arielcruzf/Wireless-Welding-Pedal/HARDWARE/1NO-M16-switch-scheme.webp

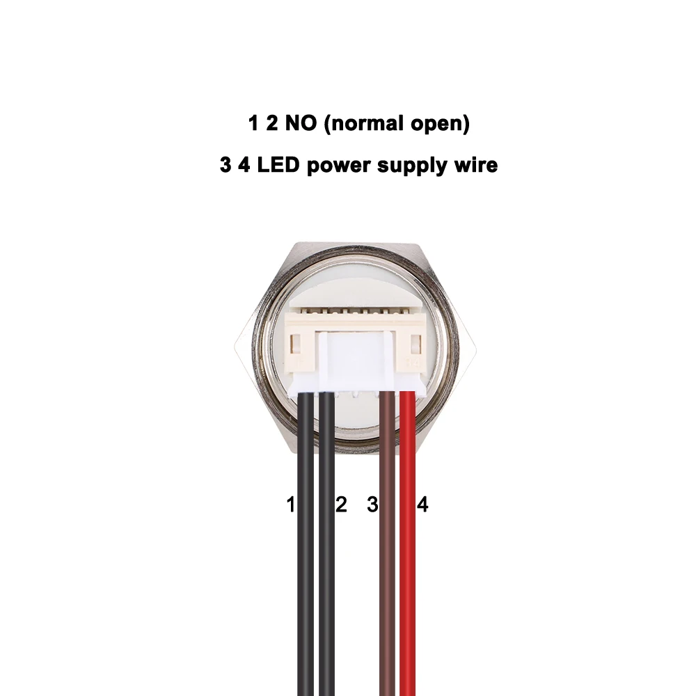
HARDWARE/1NO-M16-switch-scheme.webp
