arielcruzf/Wireless-Welding-Pedal/HARDWARE/BATTERY 103048 3.7V 1500mAh - 2.png

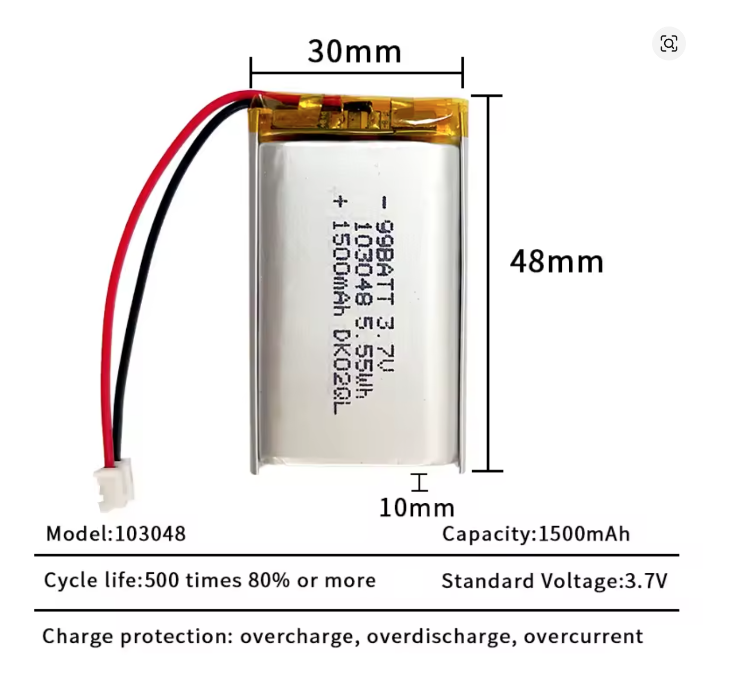
HARDWARE/BATTERY 103048 3.7V 1500mAh - 2.png
