arielcruzf/Wireless-Welding-Pedal/HARDWARE/BATTERY LIST.webp

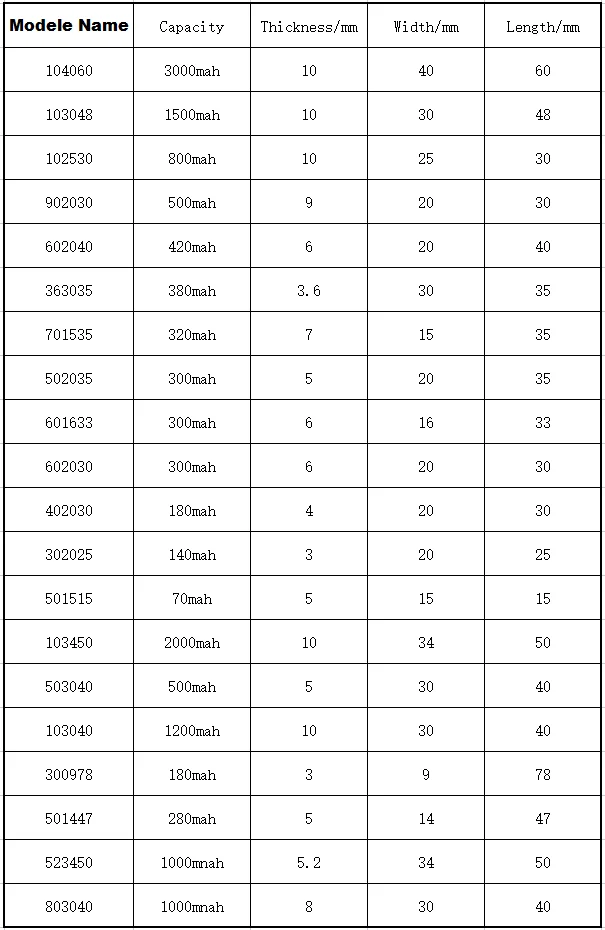
HARDWARE/BATTERY LIST.webp
