arielcruzf/Wireless-Welding-Pedal/HARDWARE/ESQUEMA.png

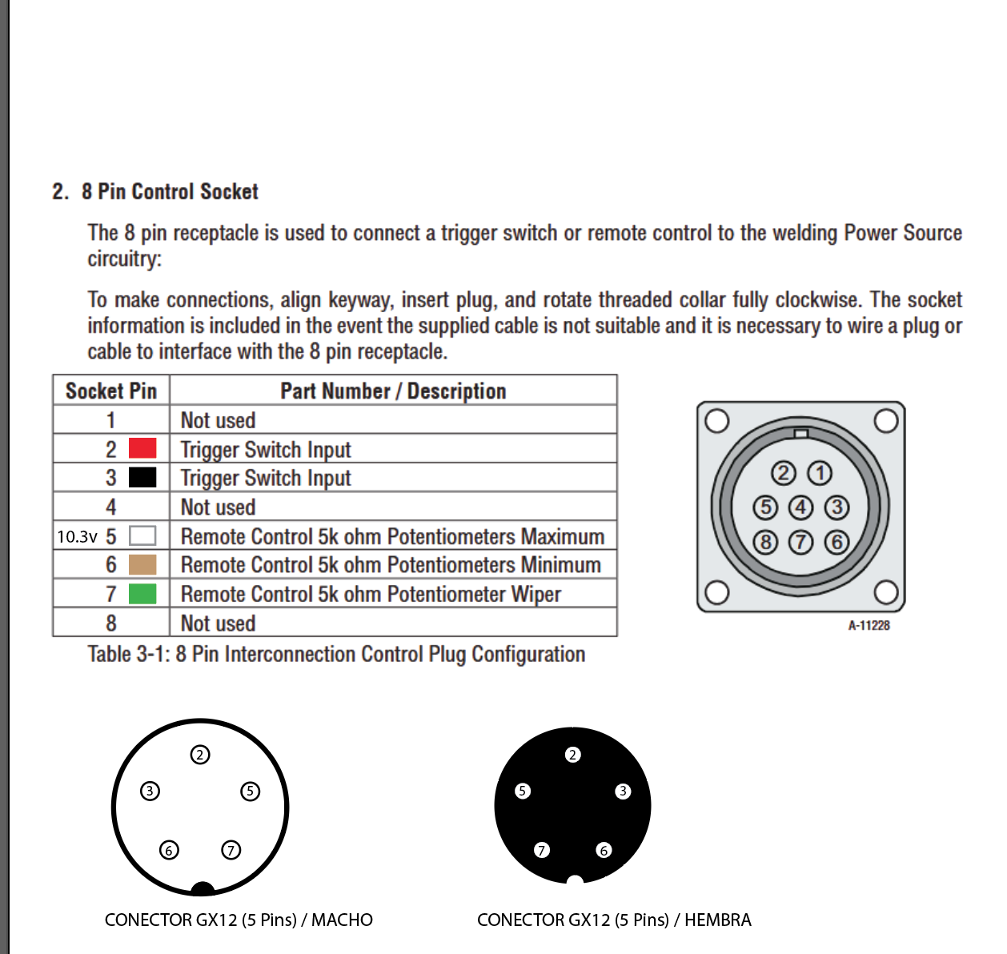
HARDWARE/ESQUEMA.png
