arielcruzf/Wireless-Welding-Pedal/HARDWARE/Flat 2D Vector Illustration - 1LiPo Battery 3.7V 1500mAh 103048.png

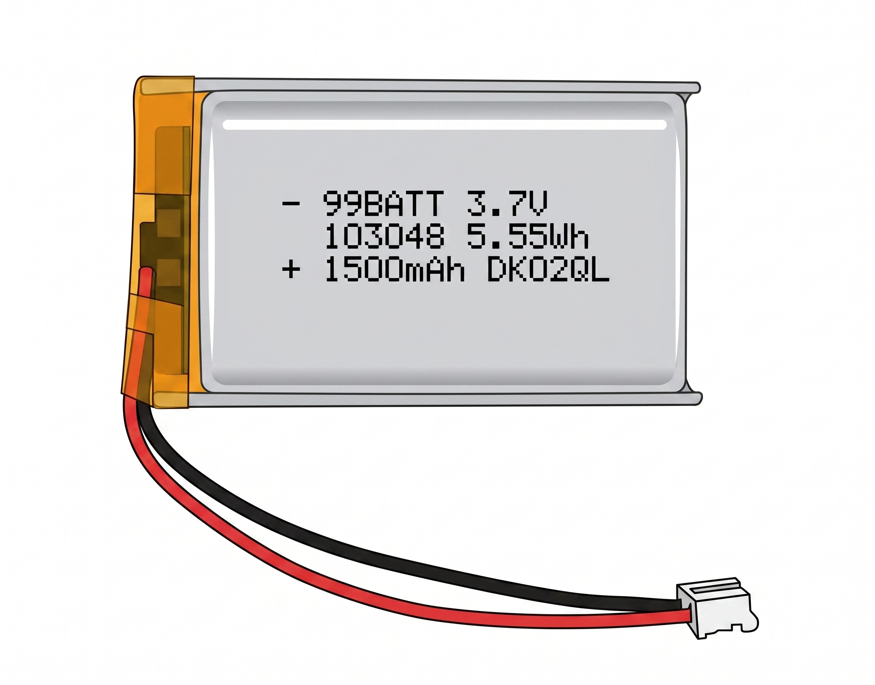
HARDWARE/Flat 2D Vector Illustration - 1LiPo Battery 3.7V 1500mAh 103048.png
