arielcruzf/Wireless-Welding-Pedal/HARDWARE/Flat 2D Vector Illustration - KW12 Limit Switch (16mm).png

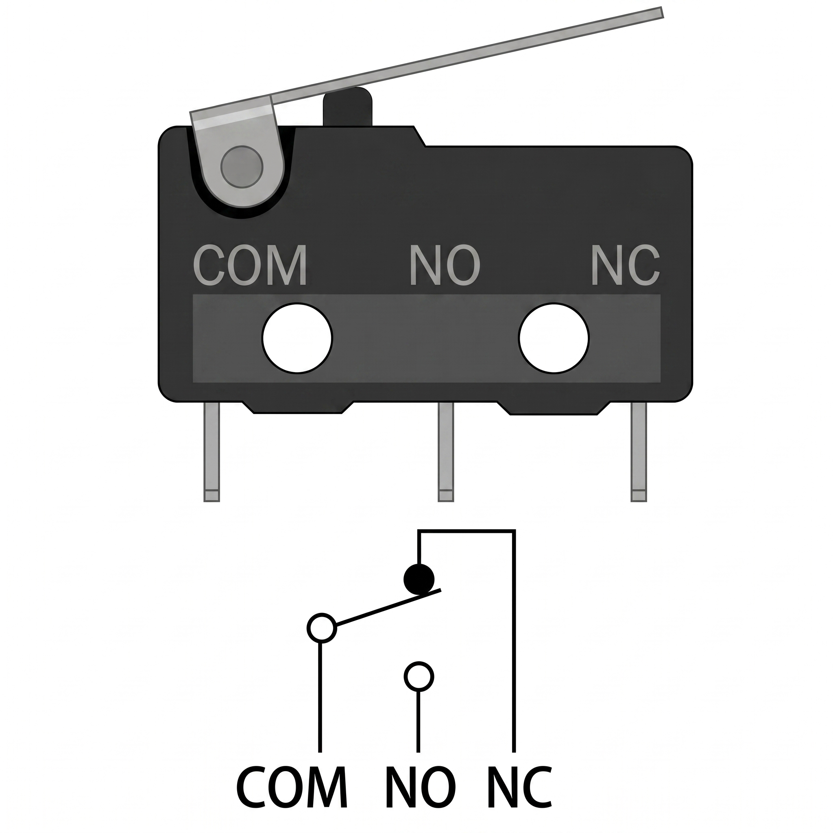
HARDWARE/Flat 2D Vector Illustration - KW12 Limit Switch (16mm).png
