arielcruzf/Wireless-Welding-Pedal/HARDWARE/Flat 2D Vector Illustration - LoRa32u4 RA-02 433MHz.png

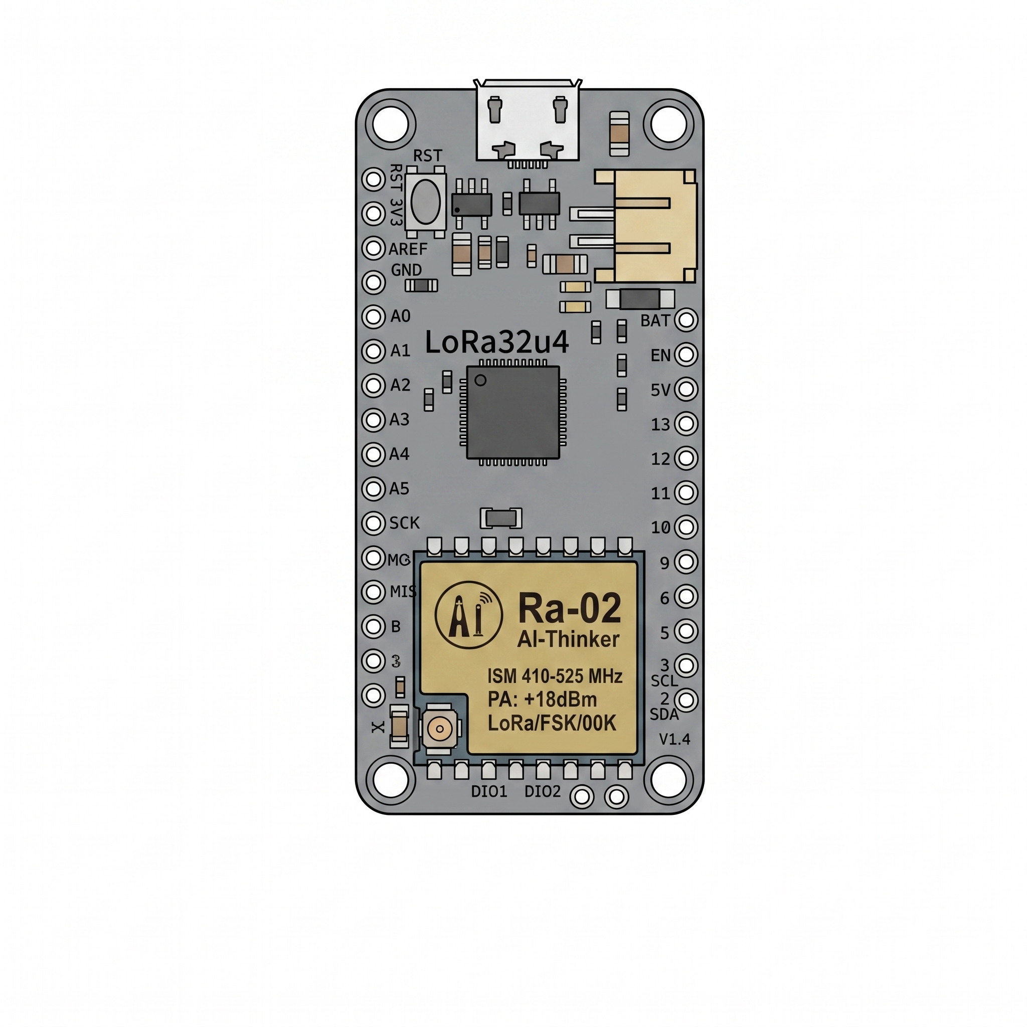
HARDWARE/Flat 2D Vector Illustration - LoRa32u4 RA-02 433MHz.png
