arielcruzf/Wireless-Welding-Pedal/HARDWARE/Flat 2D Vector Illustration - mosfet LR7843.png

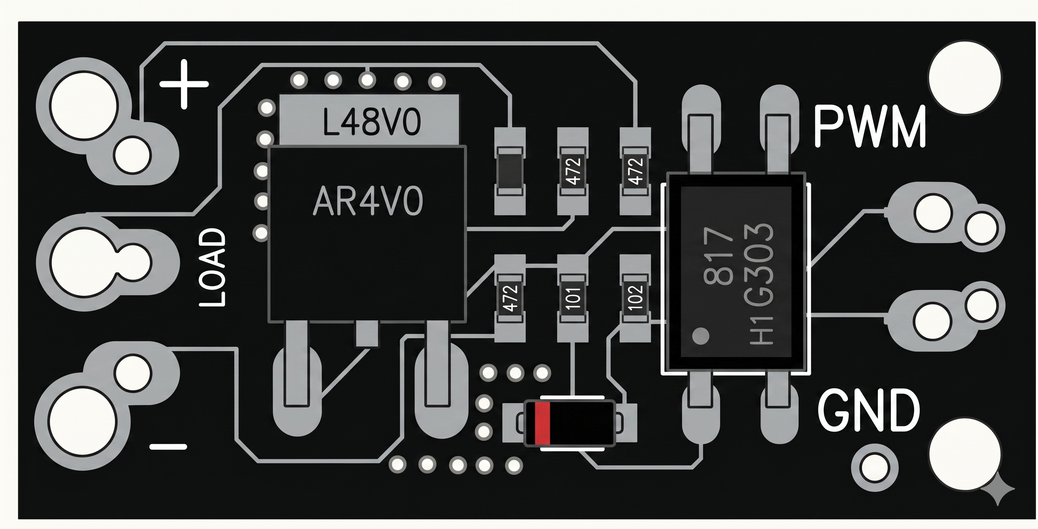
HARDWARE/Flat 2D Vector Illustration - mosfet LR7843.png
