arielcruzf/Wireless-Welding-Pedal/HARDWARE/Flat 2D Vector Illustration - OLED 128x32 SSD1306.png

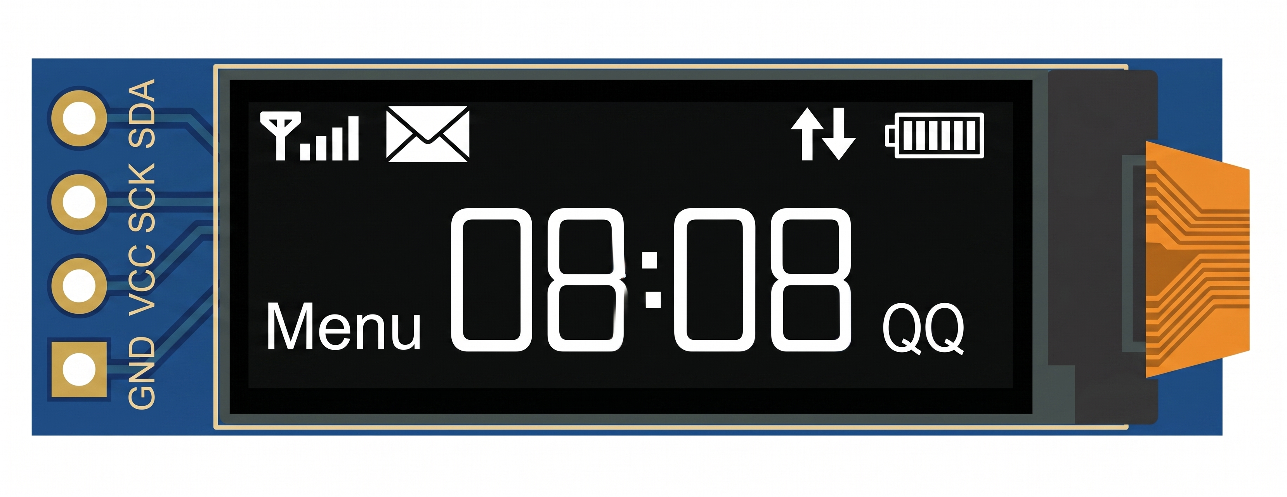
HARDWARE/Flat 2D Vector Illustration - OLED 128x32 SSD1306.png
