arielcruzf/Wireless-Welding-Pedal/HARDWARE/Flat 2D Vector Illustration - PWM-to-DAC Module (0-10V).png

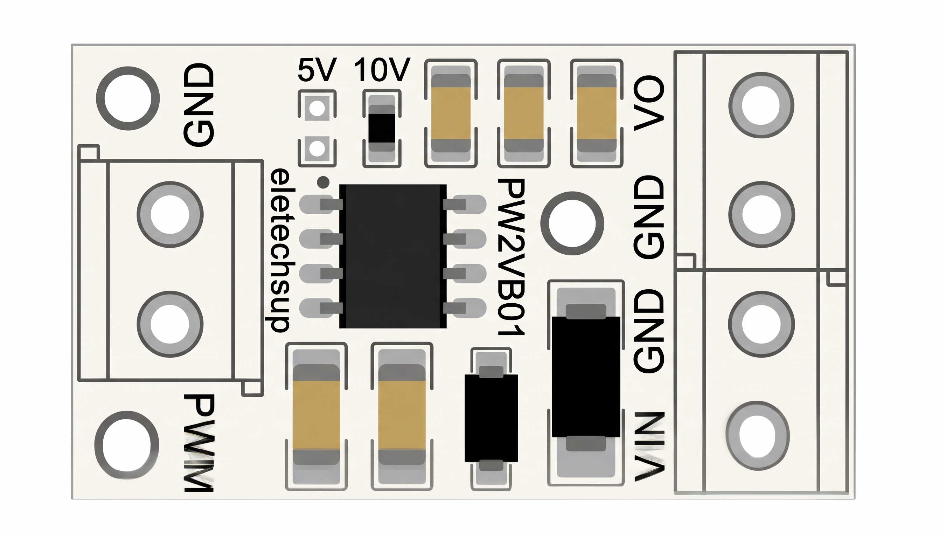
HARDWARE/Flat 2D Vector Illustration - PWM-to-DAC Module (0-10V).png
