arielcruzf/Wireless-Welding-Pedal/HARDWARE/Flat 2D Vector Illustration - VL53L4CD ToF Distance Sensor.png

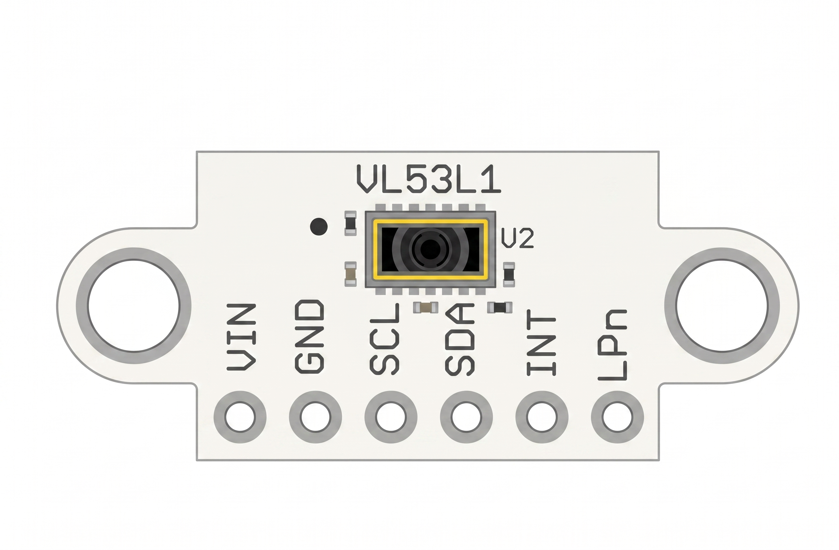
HARDWARE/Flat 2D Vector Illustration - VL53L4CD ToF Distance Sensor.png
