arielcruzf/Wireless-Welding-Pedal/HARDWARE/GX12-5PIN-M - 2.png

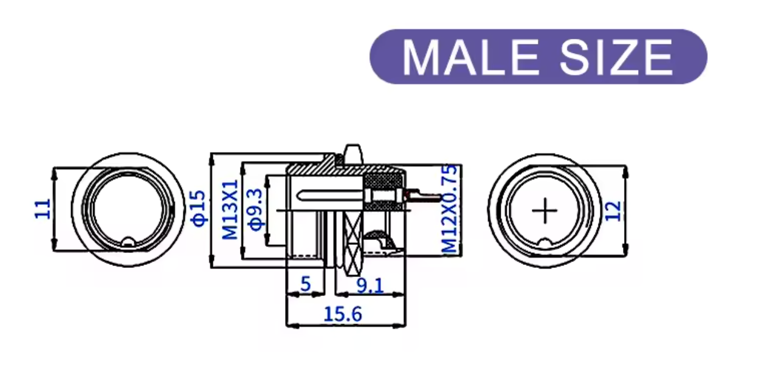
HARDWARE/GX12-5PIN-M - 2.png
