arielcruzf/Wireless-Welding-Pedal/HARDWARE/GX12-5PIN-M - 3.png

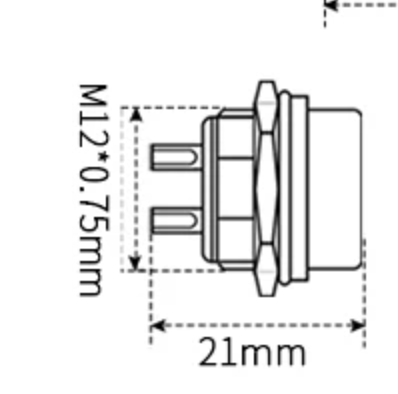
HARDWARE/GX12-5PIN-M - 3.png
