arielcruzf/Wireless-Welding-Pedal/HARDWARE/GX12-5PIN-M - 4.png

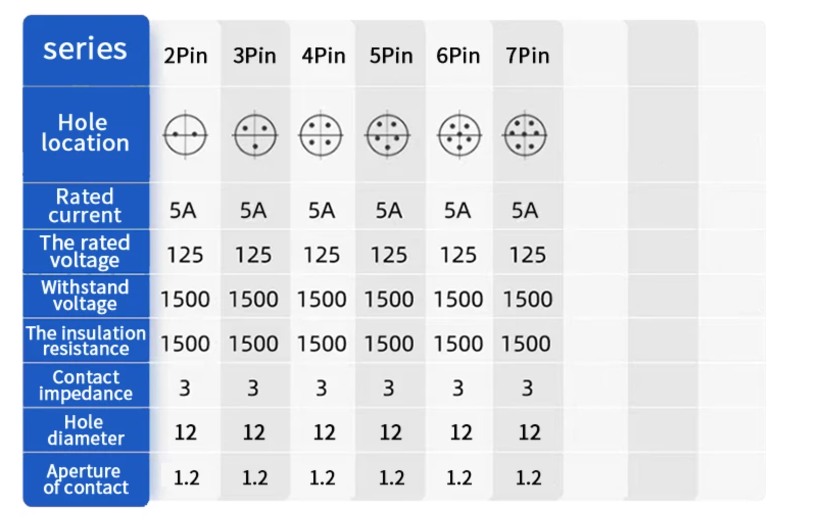
HARDWARE/GX12-5PIN-M - 4.png
