arielcruzf/Wireless-Welding-Pedal/HARDWARE/GX12-5PIN-M.png

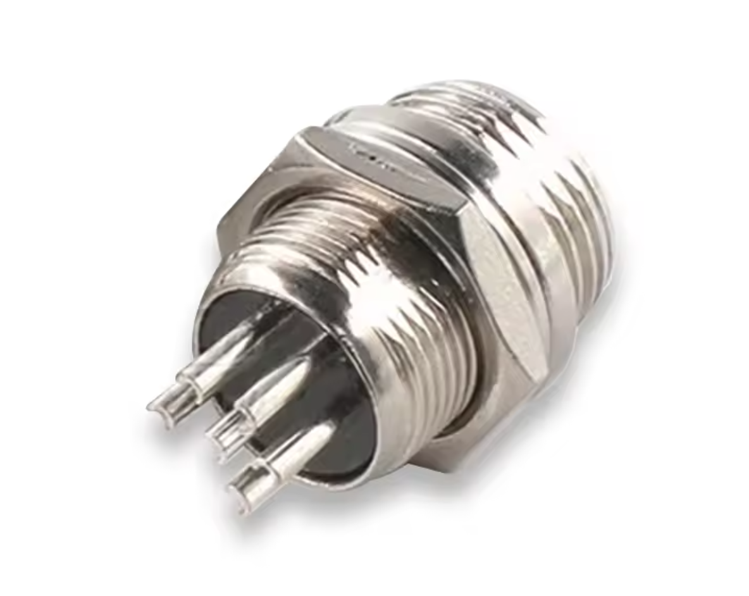
HARDWARE/GX12-5PIN-M.png
