arielcruzf/Wireless-Welding-Pedal/HARDWARE/LCD OLED 0.91 pulgadas 128x32 SSD1306 - 1.png

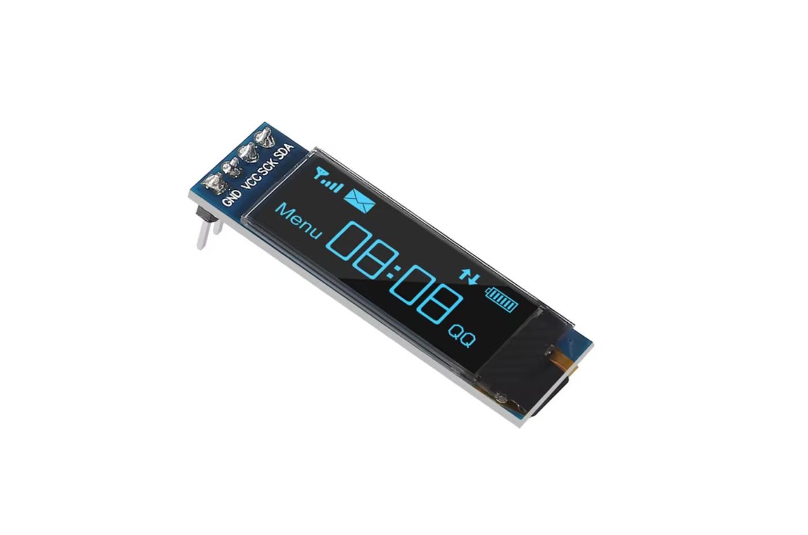
HARDWARE/LCD OLED 0.91 pulgadas 128x32 SSD1306 - 1.png
