arielcruzf/Wireless-Welding-Pedal/HARDWARE/LIMIT SWITCH - KW12  - 16mm.png

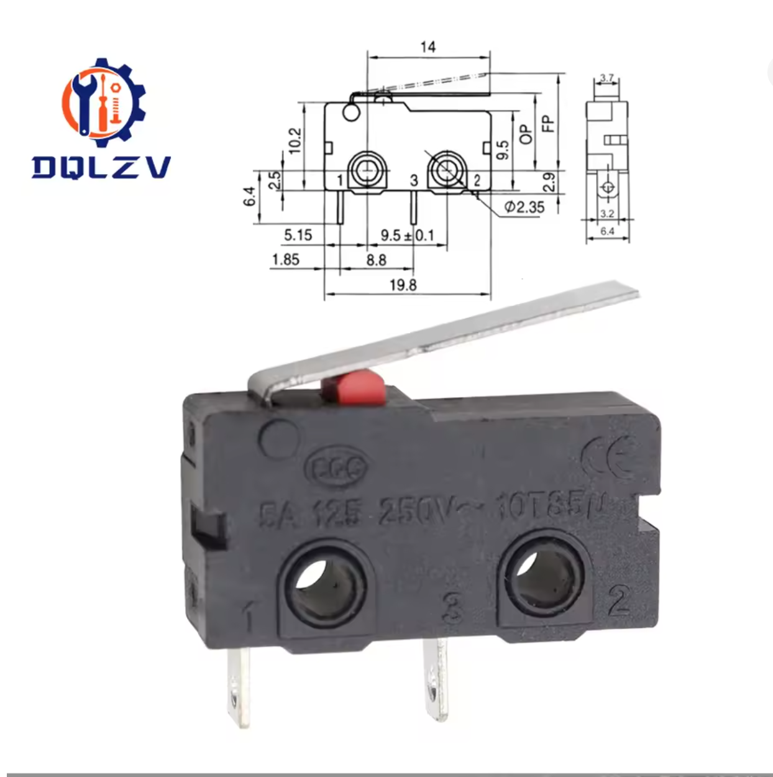
HARDWARE/LIMIT SWITCH - KW12 - 16mm.png
