arielcruzf/Wireless-Welding-Pedal/HARDWARE/LoRa32u4 RA-02 433MH - 1.webp

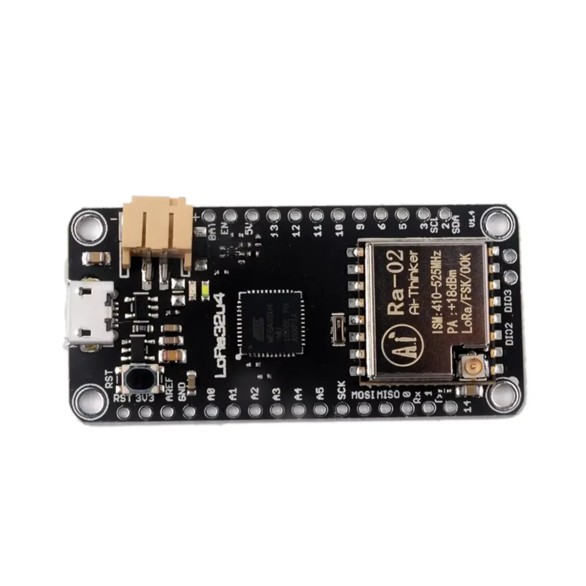
HARDWARE/LoRa32u4 RA-02 433MH - 1.webp
