arielcruzf/Wireless-Welding-Pedal/HARDWARE/LoRa32u4 RA-02 433MH.webp

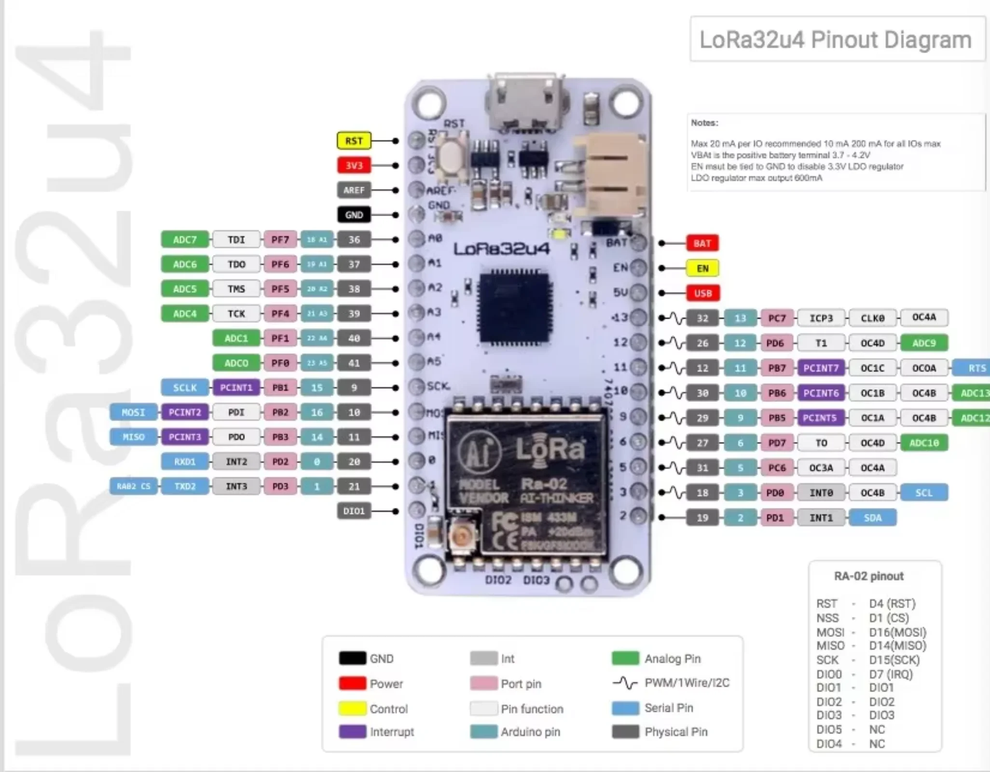
HARDWARE/LoRa32u4 RA-02 433MH.webp
