arielcruzf/Wireless-Welding-Pedal/HARDWARE/Lora32u4-scheme.jpg

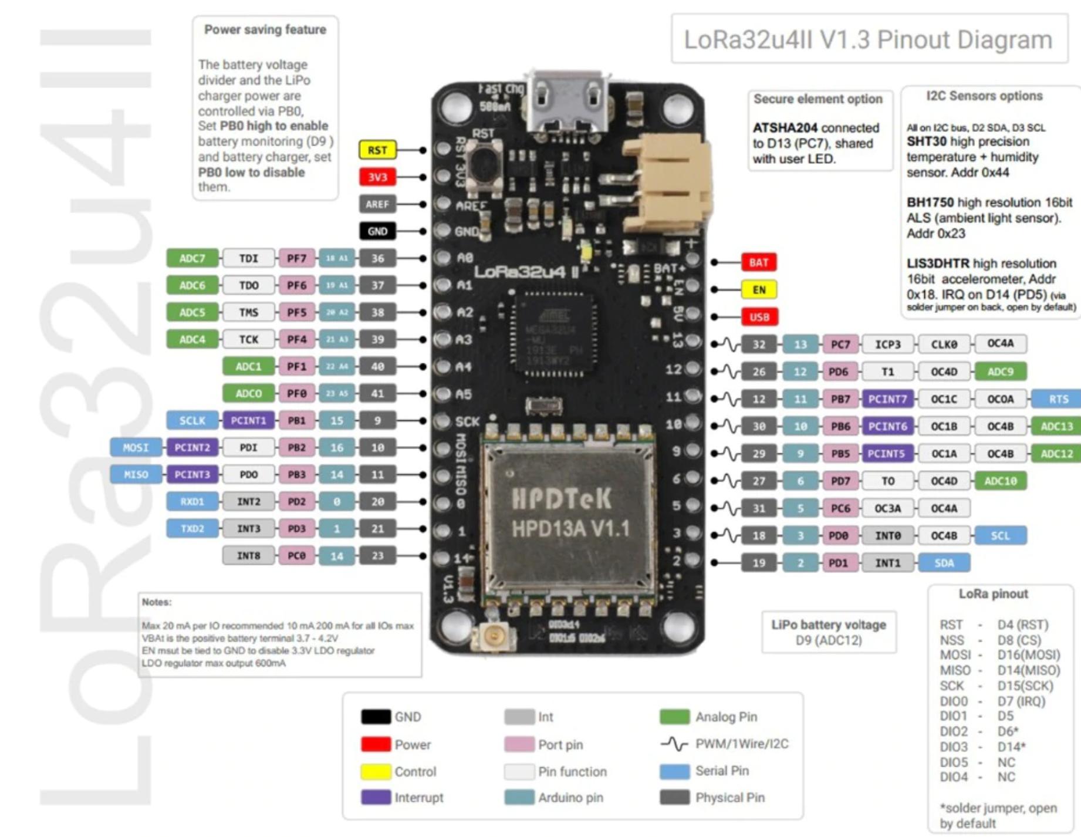
HARDWARE/Lora32u4-scheme.jpg
