arielcruzf/Wireless-Welding-Pedal/HARDWARE/P222A-1.jpg

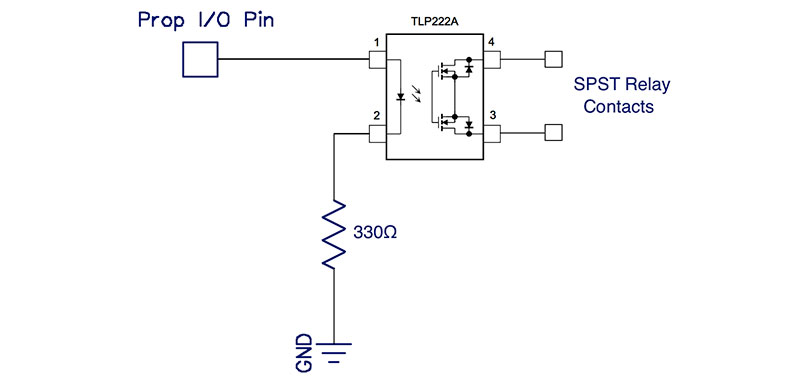
HARDWARE/P222A-1.jpg
