arielcruzf/Wireless-Welding-Pedal/HARDWARE/PWM to DAC - PW2VB01 - 1.png

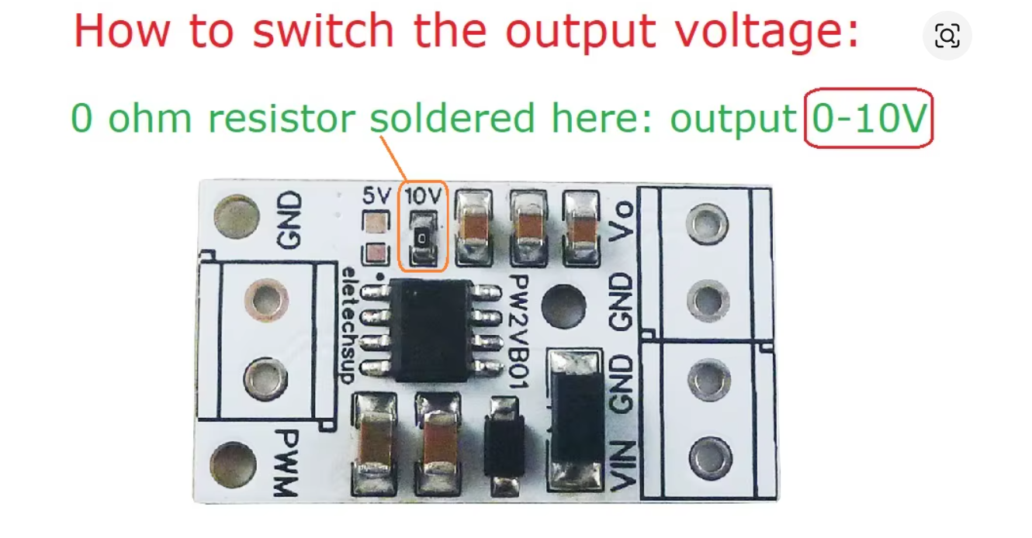
HARDWARE/PWM to DAC - PW2VB01 - 1.png
