arielcruzf/Wireless-Welding-Pedal/HARDWARE/Screenshot 2026-05-08 at 15.54.53.png

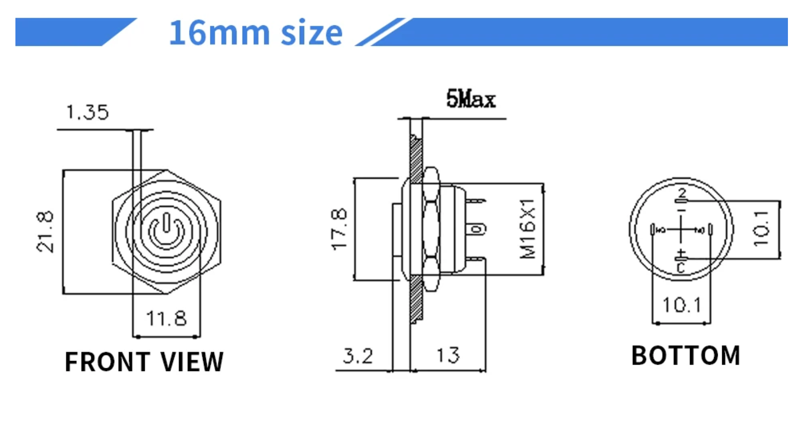
HARDWARE/Screenshot 2026-05-08 at 15.54.53.png
