arielcruzf/Wireless-Welding-Pedal/HARDWARE/Screenshot 2026-05-14 at 19.58.49.png

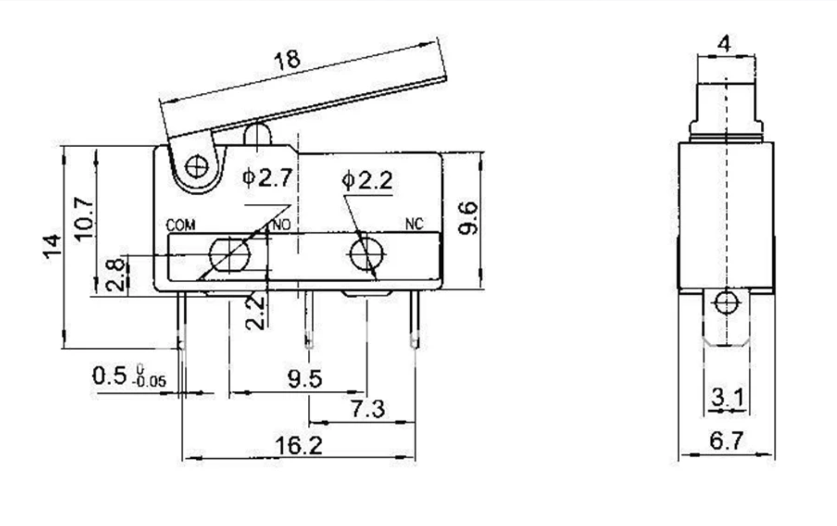
HARDWARE/Screenshot 2026-05-14 at 19.58.49.png
