arielcruzf/Wireless-Welding-Pedal/HARDWARE/TLP222A-2.png

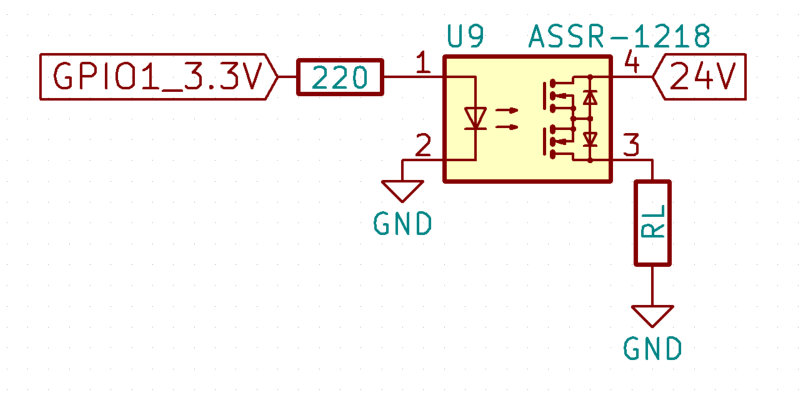
HARDWARE/TLP222A-2.png
