arielcruzf/Wireless-Welding-Pedal/HARDWARE/ToF VL53L4CD - 1.png

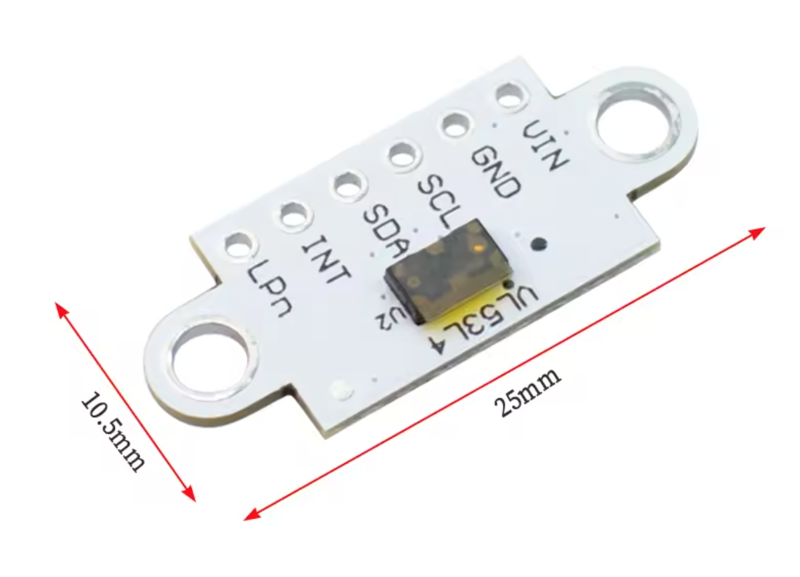
HARDWARE/ToF VL53L4CD - 1.png
