arielcruzf/Wireless-Welding-Pedal/DRAWINGS/PEDAL.SLDPRT

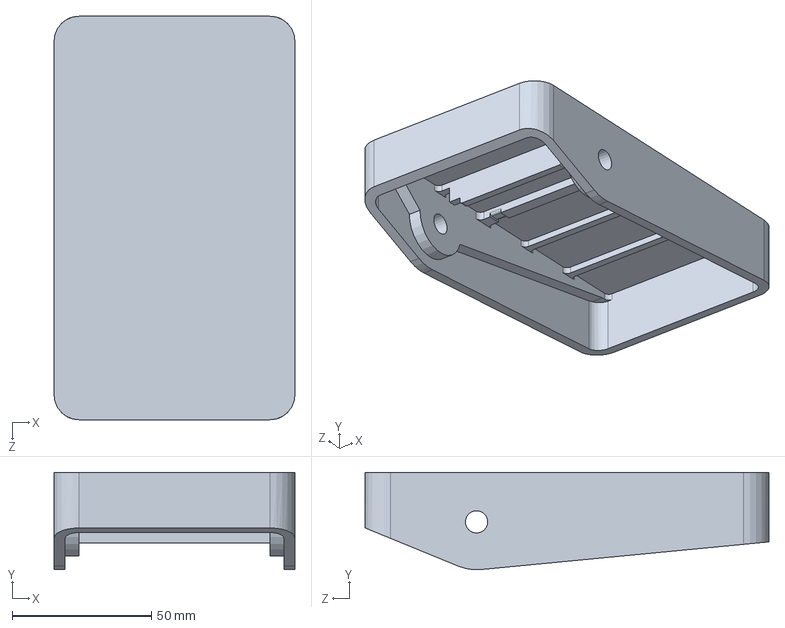
[picture p48: CAD file, 2026-05-16]
DRAWINGS/PEDAL.SLDPRT
86.6 x 35.0 x 145.0 mm
