arielcruzf/Wireless-Welding-Pedal/DRAWINGS/Sensor ToF.SLDPRT

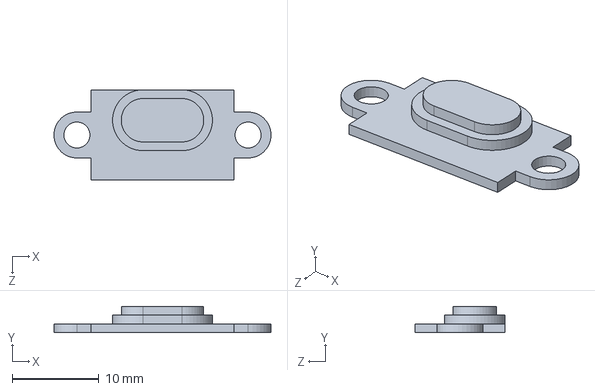
[picture p49: CAD file, 2026-05-16]
DRAWINGS/Sensor ToF.SLDPRT
25.0 x 3.00 x 10.4 mm
