arielcruzf/Wireless-Welding-Pedal/DRAWINGS/limit switch.SLDPRT

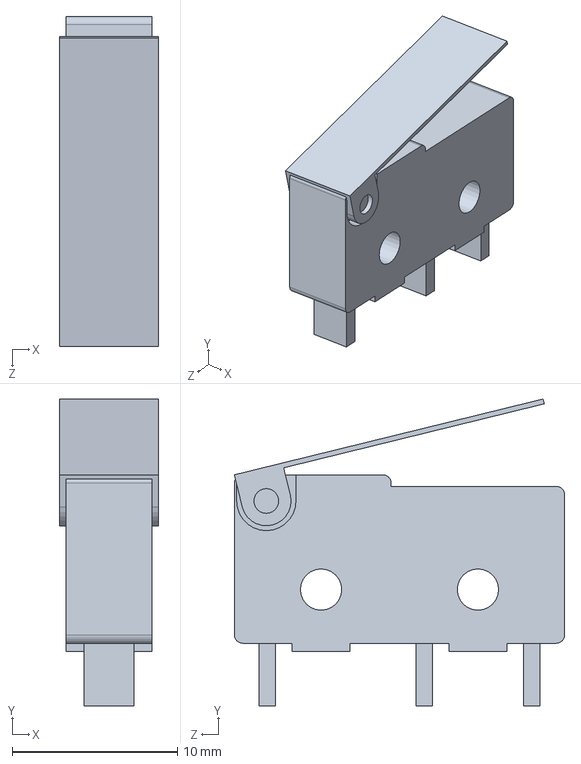
[picture p50: CAD file, 2026-05-16]
DRAWINGS/limit switch.SLDPRT
6.00 x 18.6 x 20.0 mm
