arielcruzf/Wireless-Welding-Pedal/DRAWINGS/BATT-METTER.SLDPRT

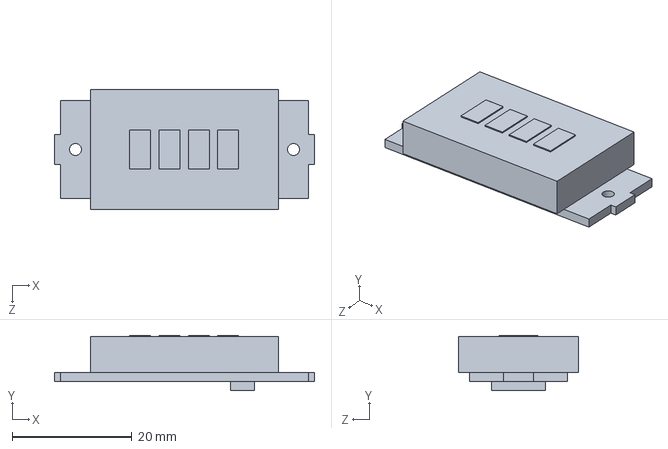
[picture p51: CAD file, 2026-05-16]
DRAWINGS/BATT-METTER.SLDPRT
43.4 x 9.20 x 20.0 mm
